VoxelTek/SkyMusicKeypad/companion/companion_assets_rc.py

# Resource object code (Python 3)
# Created by: object code
# Created by: The Resource Compiler for Qt version 6.7.0
# WARNING! All changes made in this file will be lost!

from PySide6 import QtCore

qt_resource_data = b"\
\x00\x00\x19\xc3\
<\
?xml version=\x221.\
0\x22 encoding=\x22UTF\
-8\x22 standalone=\x22\
no\x22?>\x0a<!-- Creat\
ed with Inkscape\
 (http://www.ink\
scape.org/) -->\x0a\
\x0a<svg\x0a   version\
=\x221.1\x22\x0a   id=\x22sv\
g1\x22\x0a   width=\x2240\
00\x22\x0a   height=\x224\
000\x22\x0a   viewBox=\
\x220 0 4000 4000\x22\x0a\
   sodipodi:docn\
ame=\x22SkyLogo.svg\
\x22\x0a   inkscape:ve\
rsion=\x221.3.2 (1:\
1.3.2+2023112521\
50+091e20ef0f)\x22\x0a\
   xmlns:inkscap\
e=\x22http://www.in\
kscape.org/names\
paces/inkscape\x22\x0a\
   xmlns:sodipod\
i=\x22http://sodipo\
di.sourceforge.n\
et/DTD/sodipodi-\
0.dtd\x22\x0a   xmlns=\
\x22http://www.w3.o\
rg/2000/svg\x22\x0a   \
xmlns:svg=\x22http:\
//www.w3.org/200\
0/svg\x22>\x0a  <defs\x0a\
     id=\x22defs1\x22 \
/>\x0a  <sodipodi:n\
amedview\x0a     id\
=\x22namedview1\x22\x0a  \
   pagecolor=\x22#5\
05050\x22\x0a     bord\
ercolor=\x22#eeeeee\
\x22\x0a     borderopa\
city=\x221\x22\x0a     in\
kscape:showpages\
hadow=\x220\x22\x0a     i\
nkscape:pageopac\
ity=\x220\x22\x0a     ink\
scape:pagechecke\
rboard=\x220\x22\x0a     \
inkscape:deskcol\
or=\x22#505050\x22\x0a   \
  inkscape:zoom=\
\x220.14195169\x22\x0a   \
  inkscape:cx=\x221\
718.8947\x22\x0a     i\
nkscape:cy=\x222278\
.9444\x22\x0a     inks\
cape:window-widt\
h=\x221920\x22\x0a     in\
kscape:window-he\
ight=\x221007\x22\x0a    \
 inkscape:window\
-x=\x220\x22\x0a     inks\
cape:window-y=\x220\
\x22\x0a     inkscape:\
window-maximized\
=\x221\x22\x0a     inksca\
pe:current-layer\
=\x22g1\x22 />\x0a  <g\x0a  \
   inkscape:grou\
pmode=\x22layer\x22\x0a  \
   inkscape:labe\
l=\x22Image\x22\x0a     i\
d=\x22g1\x22>\x0a    <pat\
h\x0a       style=\x22\
fill:#000000\x22\x0a  \
     d=\x22m 2356.9\
246,3386.0821 c \
-18.0307,-2.5264\
 -32.8519,-11.32\
53 -38.0379,-22.\
5821 -4.0138,-8.\
7125 -1.2572,-21\
.1465 6.2408,-28\
.15 1.8549,-1.73\
25 8.5143,-6.366\
8 14.7988,-10.29\
83 58.8872,-36.8\
399 186.8723,-14\
3.6695 311.5454,\
-260.0479 165.18\
58,-154.1956 304\
.106,-304.6548 3\
90.3248,-422.745\
8 13.6768,-18.73\
27 46.2035,-66.7\
366 46.2035,-68.\
1885 0,-0.4221 -\
4.4471,-1.0383 -\
9.8823,-1.3694 -\
19.6609,-1.1978 \
-45.9801,-8.0975\
 -62.5415,-16.39\
55 -24.505,-12.2\
781 -42.8529,-29\
.3305 -57.6894,-\
53.6164 -43.2181\
,-70.743 -90.687\
7,-163.2305 -118\
.9184,-231.695 -\
40.9667,-99.3513\
 -63.6331,-187.9\
846 -70.0574,-27\
3.9483 -1.5523,-\
20.7715 -0.6445,\
-75.9041 1.5568,\
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
      id=\x22path3\x22\
 />\x0a  </g>\x0a</svg\
>\x0a\
\x00\x00\x05\xcc\
(\
\xb5/\xfd`\xdc\x1e\x15.\x00v~\xc5&\xe0\xec\xec\
\x9bX\xb4S{\x0e\xaa\x84\xdf`p\x14X'\xfa\x8b\
\x1b\x0c\x82n=@\xc8\x16\xd1\xba\x98\x93\x1d\xc3\x18C\
\x0cB\x08\xb8\x00\xb7\x00\xbe\x00\x95\x0a\xa0W\xe7%\x0f\
\xb5\x06\xec\xcc)\x22$0j\xad\x17\x83\xc4/J5\
\xca\xbc\x8c\xf1\xf5\x96tF\x87\xdd\xc3\xbd\xc4\xf0:\x04\
;\x9e\xa1\xe9\x5c\x92@ \x10\x83\xe1\xe8\xfc?\xd2\xcb\
\xe1\xf7@\xa6ft\xbd\xdaZ\xb5\xa0R\xf6R\xd7Z\
|\xeb-pX\x81y%\xec\xd0\x1d0\xf4\x9b-\xe9\
\x0ez&\xfc\x17\x92\xdeC\x09m4\x07\xdc!\x17\x1d\
\x1dO\xd1K$\xed\x1f5\xa4\x1e\xebD\xaf\xf1\x8b$\
\x88\xde*\xd5iZ\x92\x85g\x9d\x95^\x14\xfc\x01\xd2\
\xe4g\xce\x09\xa0\xf9x\x04\x80\x04\x05\xca7\xbd\xf4\xe6\
%(n\xf0\xfbI\x1b\xd1\x82w\xa1\x97f\x93\x22\x0f\
\xb7\x9e\xb4J\x96^\x9b\x93\xbe\xeb\xcf,9\x14\x0a\x08\
\x01]\x7f\x86\x95\xaa\xe3 \xc0\xa17\xbc\x7fOM\x87\
IE\x8b:)\x13/p4q\xb4\xc0\x932~\xb0\
\xa3K\x0c\xe9\xc9\x8f\x03\xc4\xcbL\xd7\x1fN/]\x86\
\xbe\x8f\x80\xc8\xe8\xce\xbf\x07\xa4\x17\x85\xd0!\x99u\x90\
3\xf9\x0c\x03A\x97dF\xe4\xe3\xd7\x9c\xb9\x18\xa8R\
\x15\xd8\xa4\x86\xec|.&\x89\xba\xf3\x9a\xba\x9c\xd1\xcc\
P\x88\xd2\xf89&\x81\xda\x901)\x9e4\xf4\xea:\
\x04\x96\xd1\xdf\xbawO(\xea\x0a\x92CR\x80\x9cP\
U\xab\xad\xd7\xb2\xd1&A\x18\xdf[o5U\x98\xaa\
\xd2D\x11Z\xb5\xc2\x96\xc3y\xc5\xc6kQ\xec \xc7\
t\xbd\x09\xf5\x18Vz\x81\xb8\x08\x8e\x1e\xc4GO\xaf\
\xd0'\xb9\xeeZ\xec\x1c\x13\x92\xaf\x9aT\x1e\x94\x88\xee\
\xcb\xb0\xccI\xbc/gZg)\xcc\xabl\x1b6E\
0\x8a\x86'\x0f\xcc\xbb\x0d\x1cF\xb1\x5c\x86T\xdbY\
8L\xd2}\x13\xec\xe2q\x9a\x83\x15\xc1y\x99R\xc9\
\x91/\xcb\x12\x88\x97\x1b\xba\x86\x07\x91\xbd\xca\xdb2\x87\
Y\x0c\xb8\x9cq\x95\xc7\xf7\x905\x87o\xa2a^\xce\
\xa8\xbci\x93/\xb2i\x9ew\x81|[E\xf3 \xb9\
\x1b\xb0\xd3\xa2a\x1bUU+\xfd\xc1\x92^\x9c\xce3\
~\x83\xfdkJ\x8d\x01K\x91s:\x1e\xde5\x1a\x9f\
\xa9]w@\xcbWj\x91S\x08J\x8e\xe1\x84\xfcT\
\xe7\x84\xef4\xb8\xf4\xd2\x9b,\xafT\xe95-\xa6\xa8\
\x9c\xd3lP4\xb4\xbf\xecJ\xd7\xb5\xf7\xd0\xcb\x7fr\
_\xc6\xf0\x83\x92\x1d\x00\x09\x9a\x8fg X*Ra\
\xa8\x94\x04\xe2a\x12+O\x1eZ\xa79lZc\xaa\
&\x83\xdca\x0fjs\xf2\x87\x9e\xfe\xfd\xe6\x90\xbfI\
n\xd1\x5c*\x04\xf6\x0e\x8e\x1e\x14\x0dl\x03[\xbd\xf9\
vXGT\x96dF\xe2\xe2\xa9a'\xb6\xa4\x0a\xcf\
\xc9\xb4\xf6\xdak\x17urfE\xb4\xa8\xf7\xcerF\
3Z\xdc{\xadkI\x96\xc5\xd37\x86_o\xba\xc9\
\x01o-\x8a\xa4\xe4\xe2o\xe3\xb2\xe7a\x16\xebmZ\
\xc5\xf2A*]\xa7E2W\xf1\x05by[\x8el\
\x98\xd7x\xa8d\x95\xe5\xf2e[~|\x13\xcc\xcb\x14\
/gI\xc3\x83\xfa\xa6\x9b\xb3\xca\xc4\x02\x91\xf1\xbd\xd9\
\xc3\xdez;\x0d\x02\xfb,\x08\xb6\xc0]\x1a[\xce2\
-\x81#\xa8\xf18\x87\x18\x9a\x99\x11I\x92$m\x06\
\xa1\x08!\xd09\x0d\x8f:BQ\x92\x82Q\x92\xa1@\
\x0a\x11D\x08\x13$\x81\x88\x88H|\x12\x88H\xe0\x07\
\xc45=\xe0a'-\x9a\x0e\x93\xbf\xe9\xa0\xdb+\x1e\
k\xdc\xaa)\xac\x18\xf5\xc1\xd0\x81\x85\xe6\xe6I\xccV\
+\x7f_\x1d\x91jhh7\x93\xf3\xd3UK\x8a\xf7\
\xfb-C4\xed\x94.\xa7\x9cC\x1a\xb4\xe7\xd0E;\
\xc4UN\x0f\xab\x83~\xd6V\x1d(X\x83\xd1!\x8b\
\x03\x90\xd3\x92| ^\xd5\xdb\x95\xb4\xba*\x96lv\
\x8dk\xac_\x89\xecD+-\x9b\xdf\xa9\xa2:\xa6<\
1\xe6\xc1M\x95\xb3,\xe4\xaa[\x96\xe0\xbb\x8dX\x5c\
i#\xb0;\x0b\x02\x06L\xe6\x1eG\xc5\x0a{\xb9\x8b\
K\xc7\x02\x93\x0d\xe5s-\xcf\x19t\xdc\xfe\x88`\x93\
\x1a\xf3\xe5\xd2\x04J\x87\xed\x06Q-\xa7\xd3\x01\x8b\x15\
)\xfesp\xf8C\xe1\xb9\xd3\xc1\x94\xf8\x96\xd9\x7f&\
\xc8\x03\x83]FG\xe3\xd5\xa0\xa2\xa0\x00S\xc0\x04\x8c\
[\x1aC\xe7\x89\x0e\xc7\xe9\x02\x95\xb6\xd9\x08Q\xde\x5c\
\xf3\x96\x85s\x96\xd8\x81\x89sd\xafq\x17\x87\x11\x00\
\xce\x15\x96(p\xae\x5c\xa1\x14h\xf0\x0b\xf5\x98\x8a6\
\x07i\xa8\x1f-\x1cS\x94 v\x86\x17\xdc;\x86\xd1\
\x1ck\x8839\xc4q\x85\xcaID\x90\x901\xca\x9a\
]0P\x17\x1d\xf8(}\xa5\x0e\x84\xce\xf8#\x13\xc8\
\xe1>\x85\xef\xee\x0d\xe0\xef\xa5s\x8d\xa1W\x83\xf0b\
\xd1\xe2\xcf\x834\xfa\x00i\x97\xc0\xe0o\xa4ur\xc4\
\xc8\xb3\xf0\xc3\x01\xca\x8f\xdcR\xdbT\x93\x18D\xc1\xe1\
\x85\xaf\xd2\xa7\xe5\xf1\xd3\xeb\xf5\x1f\xc9\x05ZV\xc2\xef\
\xd1^}\xaf\x13\x92t\x18\xea#\x84:\x16\x82\x93\x5c\
\xefpK\x81\xac\x00 $\xa7\x87\xca\x03\xff\x11\xa0\xb6\
HEC\xcf[`I\xb9,z\x0a\xd6\xedB\xd1\xfd\
+vY\xde{\x80;\xfd\xd0g\x98G\xe2E\x883\
X\x1e\xfb\xb4\xf4\x0ed\xc4A\x1e>\xf1\xf4\xce\xc1\x94\
5\xdes\xa9=\x00>\xed\x89\x0e5|2\xbb\x02\xb4\
nFL\xfat\xbd\x1d\xff\xc0 \xd7\xa6.\xab!\x93\
\xfa\x15\x94\xcb\x5cy\xd2\xden\xf0\xe5\xbb`\xe5L9\
\x9b\xb1K\xb4\xb3t\xb3eF& \x00!\x152\x17\
x\xf3T\xa4P\x96\x93\xc9\x987\x06f\x81\x14\x80'\
\x93&6*$O\xe6\xbc\xb9\x08|\xe5\xf1 \x87\xcc\
DX\xb2\xfbm-#\x98\x86M\xa5\xb2qx~\x86\
\xe8\xba\x7f\xd0hb'L\x88\xbb3\xfb\xa0\x00\xa6D\
\xd1?PG\x83\x1c\x22n\x12ch\xf8\xe6=\xe5p\
\xec \xab\x1f\xfe\x09\xa9D\x81b\x8a1\xba\xa2\xb2\x8d\
4\xb8\xe7\x17f\xa3\x06c\xc2u\xe89\xcd\xf4\x89\x86\
0_\xd4A,\xaa;\x10\x98\xad\x02\
\x00\x00\x05\xf3\
(\
\xb5/\xfd`\xc0\x1fM/\x00\xe6\xbf\xc9&\xe0\xcc\xee\
.\x15,+\xad\x92\xaca\x19hq\x989\xfc\xc5\xd8\
\x8f\xd7{c\xe3\x01v\xd3.F\x08\xc9\x8ea\x8c!\
\x06!\x04\xbc\x00\xbd\x00\xc3\x00\x7f\x8f\xdf[,\x15P\
\xb1\xefK/n2\xdcP:\x22$,\xac\xb58{\
\xc6s\x94l\xa4}\xda\xe2\xdc]\xda\x97-~\x8e7\
\xa5\x85\xb9\xc5pc.\xc8\xef%\xc9\xe3\xf1,\x16\x8c\
\xcdyb*\xc60\xfb\xc0\xc5^\xb6\xc5\xfb^\xb6\xc0\
R\x17S\xf8\xde\x8c-.`\x5c\x01\x8a\xa5\xcc\xd8\x9b\
P43]\xda\xa5\xf8\xb9\x08\x8a\xdc\xe4H(2[\
\x13v\xd1\x8f\x8c\x8dIUl\xe4\xf7\xc4\x90|c\xec\
T1\xcc9rO\xc5V\xb2\x13\xbd\xa4+SKm\
\xc5>\xbe\xe1\xd9\xbcC)\x05 ;&\x02@\x82B\
\xf5\xbdb\xbb\xfb2\x1c{x\x9a\xb4Z\xd1\xc2W\xa9\
\x18\xd9\xf9\xe8\xc5\xbei\xb5\xd2\xadX\xf7\xdc\xfc\xbbC\
K\xcdG\x01!\xe6\xc9{\x05#\x9e!\xa4\xff}.\
\xaed\x19\x076\x80\xb13\xfe\x9f&E\x1d(\x15A\
\x96Jh\x86rDs\x04e*\xc1\x9c\xe1f\x97\x16\
n\xf2\x0e\xc3\xe3\xcb\xcb\xdf\x1d_\xb1]R\x9cf\x04\
\xc4e\x7f\x7fr\xc2\x8aU\x88-r\xed\x87\x9a\xc9\xbc\
,\x10v\xc9/\xa3\xc7\x9c[C\xa1\x01+Y\x81\xce\
I\xfe=\x85&\x89\xc2\x14\xa3\xbb\xa4\x11\xbd|F\x09\
szKB\xbd\xe2\x82\xd6<\x91\x15\xfb\x9b\x22,\xa3\
\xb3\xef\xff9\xe2\xb8+\xb8\x86\x7fB\x0dEe\xed\xb5\
\xf8\xbaQ\xe7\x9e\x9c1\xb6\xb8\x9a\xaaLYi\xfa\x88\
\x97\xad\xf2\xd5x_\x911\xf78\xfe\xd0[\xfe\xce\x88\
\x1b#\xda\x8ay\xfc\x18bL\x8f\xc7\x98\x15\xa38\xb9\
\xdf\x01\xe0\xe5\xc8\x16\xba\x8a\xc5iM\xdb `\x15\x99\
4$\x11\x1e\xa8e\xba\x83|\xa0\xd66\xefR\xd97\
\xe1\xb8lzd\x92-G\x1a\xd9\x87\x1b\xbaLr;\
\xed\xb0\xd7\xa3t\x19\xc4\x03#Y\xe5\xeb6\x87+\xa2\
\xfb\xb4d\xa2\x1f\xa0\xa6!\x8eO7x\xd6\x07\xa1\xbf\
\xea\xe3t\x97Q\x0c:\xadu\x93\x06\xf8\xa07\x070\
\xb2e\x9f\xd6(\xcdm\x11\xf0\xc1m\xdfWq\x80\xdc\
d\xfb\x1c\xda\x1b\xb8\x13d]\xab\xaal\xb5\xcf\xb0\xac\
\x98\xe6\xfb\x8b\xd9\xc3\x7f\x92\xe5\xb6\x84e\x1d\xbdf\xc3\
\xf1\x9f$\xcd\x8b\xfd{\x13R\xc0r\x8f^BPz\
\x8b\x86\xc2\x9c,\x9d2\xa6\x06x\xff\x903\xb1;/\
\xb1d+6AST\xd2\x89Z\x1fk\x9b\x95>\xf1\
\xfe69\x15\x0b\x00\x09d\xc7\x5c \x5c\xea1a\xb0\
\x14\xc4\xf1e\x90KG\x1a\x9b\xb79p\x9b5U\x93\
\x81\xf6\xb2\x06\xd5=?EN\xf7\x8e\xb3sO!'\
\xeaR\xd4\xdd\xddw\xc6eDe\xc9/\x12\xf4\xb2*\
\x8a\xb2\xf9\x92,\xca\xb2*\x9c\xe9\xbd\xae\xadr\xbe\x17\
\xb2TC+\xe8\xbdQ\x04Q\xd9R!\x85\xaak)\
\x84-{]\x93\x84/\xcd\xe8e'\xa9\x820\xc6\x17\
\xbe\xa4\xeb\xe6\x09\xc4\x88\xe7\xcex\x93C\xee{\x1c9\
\x04g\x90\xeb\xf4\xf7e\x94\xfbq\xdb\x84\x02:&\x9e\
\xb7=tgs\xc5q}\x9c~p\xd9g=L\xb4\
\x8aR\x015N7\xc0H\xf6i\xc9\xa75\xa4\xa1A\
\x81\x13\xd6\xda$B\x81\xd0\x19c\xadq\xb1\xc5\xde\x06\
\x91\x05\x81/\xa8\xf18\x87\x18\x9a\x99\x11I\x92$m\
\x06\xa1\x0c1\x10:\x0b\x8f:2Y\x14\xc2A\x12\x81\
@\x08\x19D\x08\x13$\x81 \x12\x88H<\x22\x12H\
\xe0\x07\x84*= a\xef\xee.\x1d\x83\x1f\xae\x92.\
\x5c<\xa0q\xc1\xd1t$\xea\x83\xc3\x93\x1e\xce\xddN\
\xc2\xbd\xccQ\xfd*\x17:\xa3\xe1\x1e\x82\xdc\x86\x19\xca\
<1\xdc\x02%\xcd\x08\xfa\xb4\x98T\x11<\xa7\xe5&\
\xdb\x87{\xad\xcc\x5c\xfe\x08\x0a\xe1j\xea\xb8\x03Wq\
\x0b\x11\xbe\x7f\xcd\xf0\x0d\x80\x0e\x96\xa2\xfc%\x93'9\
NJ6\xd3O\xab\x22~\x898\x10fk)j\xa0\
\xc4h\x09\xb9&&\xbb\xc9\xef\xb4d\xb7J\x1eq\x99\
\x93\x92\x9cH\xd2\x9dRQ\xc7\xd4NX\x14P\xbfb\
!\x0bi\xeb\xaa\x12V\xb7Q\x11\xd7\xd9\x08\xef\x0e\x83\
\x80\x01\x99\xb9\xc6Q\xb1\xc9^\x0e\xe2\xd2\xb1\xf8dP\
\xf9l\xc8sL\x8f\x1b\xd2\x11\xde\xa4\x06x\xb9\xe4\x02\
\xa5\x1bu\x83\xa8\x96\xd2\xb9\xc2\xc2/\x05\x7f\xce\x0e\x7f\
('77\x98\x19\xdf2\xe8\xcf\x1ay`\xb7\xcb8\
\x1a\xdd\x0e\xe2\x0b\x080WL\xc0\xb8\xa51\x5c\x9e\xeb\
\xe10,P\xc96\x1b\xf9\xe4\xcd\x95\xec\xb2\x18\xce\x12\
V0\x81B\xf6\x1av\xbd\x8c\xb0pxY\xc2\xc2\xf9\
\xe5\x0c%\xa7\x11\xbcP\xa3TPs\x90U\xfd\xb0\xe0\
\xd0\xa2\xc4n\x87{\xa1\xbbc\x1b\x8d\xb1\x06q&E\
\x1c\xa8P1\x89\x0a$d8\xb6f\x17\x8c\xf4\xa2\xcf\
\x1f\xedW\x8e\x81\x10\x92\xc7\xbc\xe4\xd8\x81B)xc\
\xd2h\xa5_0-q\x90\x97\x8f\xf6?\x0f\xddt\x0f\
\x09.\x81\xd2oPu&\xec\x96'\xf4\x87\x03\x88~\
\xf8\xc1Q3I\xf2\x16\x14\xbd0/z^>>\x9d\
Y\xffa]P\xcc\x8a\xe8\x1eU*\xe8u\xe4\xd2\x84\
\xa1&Bwc!\x89d\xf8\x8e\x99\x14 \x05\x22\x22\
{\xfa\xbd|\xfd\x1f\x05UG\x8a=\xf4\xb0\x05\x97(\
p\x15\xd2Y5\x17j\xe9_\xcc\xe2\xbf\x17\x01w\xc0\
\xad\xcfj\x1e\xce\x8b\x18N\xa1\x5c\xe4S\xd5;\xdc\x10\
\xc7\x9c}\xe2\xf0>a\xaaoT\xa4[[\x06\x1f\xf8\
\x84\xec\xfa\xbd\x9f\xdd\x00\xad7\x22fu\xba\xe2\x8eH\
\xc1@hS\x99\xd5\x90L\xfdzr\x99/'m\xde\
\xcd\xb3|GVd(\xa73\x96\x01\xbbJ\xb7\xa3\x8c\
\x07\x04\x06@\xa4\x22u\x01`\x9e\x0c\x8a\xa4\xe5\x04\x18\
#\xc0\xf0Y\xf8\x01\xae31b+G\xf2\xcd\x1c\x98\
\x0b\x91\xaf=1\xe4\xcc\xcc\xad\xa5\xc4o\xe6\x0c\xcc\xb4\
\xc3\x14\x94\xb5\xc1s0\xc4\xeb\xc4\x84\xf6\x09\x8b\xf0/\
\xee\xf6\xec\xa0\x05<$\x0a\xf8\x01Y4\x06\x90b\x93\
\x989\x0d\xab\xbc\x8ar\xe8:(\xecG\xfd\x84\x07Q\
\x00\xac\xf8\xa0\xaeT\xb6\x93\x82\xfb|\x03\x9ck\x94L\
\xa8\x0eK\xa7\x1e\xfd\xd3\x10\xfe\x0b6\xc8NE\x07b\
\xb1U\
\x00\x00\x06;\
(\
\xb5/\xfd`\xe1 \x8d1\x00JB\x08\x0d)\xc0j\
\xec\x0eC\xf32\x1a\xb8)\xffY]\xabe\xb0\x5c\x8f\
\xfet\xd9%\xde;\x95\xd2\xcfeY\xe8\xed\x0a\xaa\x08\
\xb0,\x82\x00\x83P.\xc4\x00\xc3\x00\xc9\x00\x98\x0e\xfe\
9e\xc6\xb0o\xbf=\xdf\x19h\x0e0'\xdf\xc5\xde\
\xed\x8f\xb3H\xe9!$ (\xa5\xf6b\xbc\xd1{\xa8\
Si\x15b\xdc\xfc\xd9\x94\xdd\xf9K\xff\x0f\xe2\xef\x8e\
\xb3|\xc4\xe7\xfb\xf3`0\x18\x04Ba\x19GpN\
\x8a\xcf\x07P(eS\xbb\xabD\x0b\xd0\x5cm\xb6\xb5\
^Km\x01E\x15 \xeds\x15\xdb\xc2u\xbf\x81?\
\xe0\xd8\x19\xb6.\xfc\x17H\xa6aW8\xdeuOa\
\xf9yN^XG\xf0\x0b7H\xf1\x9c\xc0\xd1\x0b1\
\xd3\xd2\x87b)=\xd2\x95T\xd29=\xf4\x05f\x87\
\x0eRJ\x00\x9f\xc3G\x00\x90p`v>\xa7\xcd\xbb\
\xc8y\x9c\x1b\xbf\x9c\x91\x83@\x9b\xcc\xe9\xe3\xa1\xd7;\
\xbe\xe5\xa4O\x9d\x13\xef\xe1\xf7\xdbA\x8a\x95\x87\x03\x08\
\x01\xd1C\xb4\xff\x84G2\xbf\xffeN\x7f\x0c\xf9\x04\
\xecF\xce\xc1\xfd\x1e\x11\xf5\xa1\x0a\x034\x80b7t\
?\xfe,\x15dv\x1a*!\xf26\xd7\x91\xd7i\xae\
\x84\x80#g\xd9\x22C\xf8C\x07\x05\xa6\x8b\x14\xbf\x1d\
\xfa\x9c\xb6\x98\x19?\x03:\xa7\x05\xca\xf6}\xbcps\
\x9a\x0b\xbb\x0b+\xcfU\xf0\xa7 \x10\xb6\x18R\xbc\x0e\
\x8e\xbb\x22\x9b\x01\xf4\xa1\x02x\xf8\x85\xbe\xcb\x06?\xd9\
\xcaInQ:\x92\xf2\xe0%\xcc\xda!\xe47'\xbf\
3\x9c\xe8\x8c|{\x7f\xe9\xbc\xfd \xac\x84\x0f\x5c%\
\x03QZ\xa9\x95\xaa\xc3C\x0c\xae\x11\xc5\xf9\x812\x96\
JP\xad\x0f\xbeNwq\x8e\x129\xf1\xe49Uz\
\x7f\xd0\xf0\xb7\xe7y\xae3\xf8\xdd\xd0m\xb0\xa3s\xc2\
t\x8f\x03\x7fy\xc3VW\x91\x87dA_k\xabE\
\xb5\xd4f\xd6\x02\xb5I\x0c\x0a\x016\x89.]U\x96\
c\x83\x1e\x91\x05\x84A\xb6U\x94\xc6\x1c\xda\xa6++\
\xab\x99\xd2\x22\xd7E\xe1\x06\x05\xb1\xeecAiV\x01\
FA*\xa6\x19\xb4f\x12\x8crd\xdb\x83\x9ah\x98\
\xa5 1\xc04\x0d\x89\xe8\xc6Vi\x07C\xd3\x0a\xb2\
H[\xd0\x1a\xa4]\x1a\xa3$\x09LWXd\xb1-\
\xd0\x96\xc2\xf6\xb0(MWY_\xd6ck\x5c\x96\xa6\
M\x18\xdb\x15\xb14\x86\xce\x06T\xdcD5\x82 \x0a\
\xed\x91\x13\xe7T\xf1\x9d\xf29\xe7\xc7O\xdc\x0c\x9c8\
\xe7T\xb1\x5c\xba\xff\xbeO\xa1~[8\xc9&n\xaf\
C\x08\x88\x9d\xa1\x92\xf9\x98J|\xadL\xd8\xed\xb9\x8b\
\x83\xcdC\xd1>tN\xb8\xc1\x8e(\xb1\x0c\x00\x12>\
\x87\x8f@\xa8\xb9\x11I@\xb3\x83\xa1Q\x0eI?\x16\
Vf)\x5cV\x84!\x9c\xd0\x19\xb5\xc8\xbc\x87cw\
\xe1\x9d1\xf2\xb0K>lk\xcdY\x8a\xa0\x9c\xa3\x1c\
E\x90\xbd\xb2J\x95B\xf7\xd6\xea8M\xbe\x99\x83*\
\x95\x8d\x8d\xa8$\xe1\xc7VII\x89\xe2\x07\xca\x19\xce\
{\x0e\xfc\x9c\x97\xa8\xd1\xad\x9bw\xae\xa8\x0aG\x14C\
J\x03{qT\xe5\x95\x1e\xe8\xca\x87\xac\xd5V[\x1b\
*+\xf2\x81\xd3Pk\xa5(\x1d\xe94\xd6Z\xc9J\
\x8fT/\xde\xc0n\xdc\x0d\x19V\xb8|{^\xe8\xb0\
w\xbb0\xadi\x94\xa4j\x97\x15\x91l\x8cH\x96Y\
\x0d\x8d\xd1;aH\xda\xa5\x1b\x17\xa5E\x0b\x22\x15$\
\x99l\xd5\xa5\x17\xdb\x83\xd24D\xd3\xda\xa1`\x11\x81\
B\xa8\xf1<\x87\x18\x9a\x91\x11I\x92$m\x06\x91\x08\
1\x10:\x0d\x8f:BY\x16BY\x10\x82 \x84\x8c\
!F\x09\x92@F\x02\x11\x89GDD\x827\x84\xaa\
\x1e\xf0\xb0\x99\xf8\xad\x0e\x17\xcaM\xcaMO\x8f\x8d\xb9\
\xd6\x89L\xc0\xfa\xb8w\x1b\x83\xdf\xa9I\x02\x8c]\xaa\
\xee\x95R\x9c\xa2\xb9=\xc4\xbf-ER\x06<iK\
8\x07g\xaam'`j\xce\x83\xc0]\xd4\xf8\xea\x8e\
\xff\xa4\x02|GZ}\xd2\xc8I\x01\x91Y\xb0g\xb3\
\x03TW{\x7f\xcb\xc7G\x14;k\xa5\x930\x8e\x1e\
\xbb!t'8o\x1fy\xae\x14l{\xe2\x94\x0d\xfd\
\x9ao\x18\x91K\xcc\xd2L\xa5\xd3\xce\xe7\xa5\x22\x1c!\
p\xdf\x0c]\xdfM\x5cu\xec\xe1\x03@\x15\xb5\xa5\xa6\
+X\xbd(\xe5\x8a0@\xa2\xfd:\xa8\x0b\xea\xae'\
\xa9Z\xc9H\xc0,\x01\xd7\x98\xd22\x9a\x13-E\xf2\
\xbfS\xdf\xd71\xfd\xe4\xf2\x07\x95\xaapc!\xe2n\
B\x82\xef6\xd2\xc8\xed\x14\x04w\x17\x84\xa0\x01\x999\
\xa9Q\x01\xc2^.\xe3\x0c\xb2@\xc9w\xf0\xb9\xc8s\
\xb6#7\x88!\xac\xa9\x86\xd4\xbe\x8c\x02\xa5{\xdb\xb0\
\xae\xf6\xce\xb5c\x81\x8cB\xa3k\xe8\x1fj\xc4\xe9\x1d\
\x86\xe4[\x8c\xd6\xe7G\x0f\x04p\xa3\x89\x9e\xb8\x83<\
J\x00\xe60\x09\x98\xb50\x86\xe3\xcd#\xe7\xc3\x02\x95\
\xb6\xd8\x08\x91\xde\x5cs(\x0b\x9b,\xb1\xb0\x09Dc\
\xafmg\xa2\x084\xf7D%\xda\xdc\x13\xd5\xa3p\x1b\
\xc0\x81\x9aU\x05Q\x07\xb1\xbe\xc7\x84\x1b\xc9%\xaf\x1d\
\xc9\x05\xc2]\xaeh\x80\xf5\xab\x99\x1crtY\x05\x12\
\x11\xac\xc8X\xc6\x86\xb8`x\x8e\xf6}\xb4\x9fR\x07\
\x84\x001&B\x8e\xb1\x0c\xd6\xff\x8dA\x82J\x7f\xc0\
d\xbbI\xb0\xc6\xf4\xe5y8\xa5\x84K6%h\xc2\
\x1b\xea\x1dU\x82\xe1\xc1\xe6\x81\xf4\x90?\x8a\xe0\xe8\x99\
$\xbb\x05\xe5,\x8c\xd36\xc8C\x9bV\xc1\x7f\xf0\x16\
\x14\xb7\xa2\xc6\xa3\xa4\xfa\xbfNP\x12\xccP\x1b\xa0;\
\xd2\x90\x88d\xee\x0ee\x0a\x10\x03a\x02;=\xb0<\
\xc3\x1f\xf5j[\xaa\x15*N\x0bT\x10\x0d'\x13-\
\xb7\x16U\xff\x90\xac\x09\xfc\xbe\x10\xb8\x0b\x1e5\xd3\x0b\
\xb1w\x86\xcc\xc3\x98\x16\xb5#DL\xe2\xc6\x1b_\xe3\
\x9c\xa7\x1e\xe2w\x17\xb5\xd3\xe4\xfb\x9e\x88\xa8\xae[\x9b\
\x03\xec\xea\xbaah\xd2\x5cuB\xae\x0d\x1an\xbe\xbb\
\x01R\xf8\x89\xfd\x1fA/\xe32\x90\xb6\x909\x1f\xdf\
\x1f\x8a\xf0\xc9\xc9\xca\xfa\x0b\xe9\xf9Q\x18\xe1Q\xd8-\
C\xc8v\xb9\x5c.\xa01\xd2\x18\x9e\x0b\x06 \xeaL\
\xbe\xb19\x9340'\xc9\x05\x87\xd7\xcc\xf8x5\x17\
ji\xe16X\xa6\xf3\xcc6\x1faW\xf3\x8c\x07\xd1\
;\xf1\xd1>Q2\xec\xc4\x9dG\xbb\xda\x80\xa4D\x09\
?@EFa\xc4\x8a\xf6\x05\xcf!(V\x84B\x98\
\xe3S?b\x0e\xc8\xac\x82d\xc5d\xe5Te\xf9\x0b\
\x1a\xdc\xbf\xf1\xde6\x00\x89G\xc2\x0c\xc8\xa3o\x182\
\x7f1\x0e\x0a)\xcb\x81\xa4k\x15\
"

qt_resource_name = b"\
\x00\x08\
\x0c\xdf\xacs\
\x00k\
\x00e\x00y\x00I\x00c\x00o\x00n\x00s\
\x00\x04\
\x00\x075\xdf\
\x00l\
\x00o\x00g\x00o\
\x00\x06\
\x06\x8a\x9c\xb3\
\x00a\
\x00s\x00s\x00e\x00t\x00s\
\x00\x0b\
\x05\x96\x06\xa7\
\x00S\
\x00k\x00y\x00L\x00o\x00g\x00o\x00.\x00s\x00v\x00g\
\x00\x13\
\x0f\x14:\x07\
\x00s\
\x00k\x00y\x00M\x00u\x00s\x00i\x00c\x00_\x00s\x00q\x00u\x00a\x00r\x00e\x00.\x00s\
\x00v\x00g\
\x00\x13\
\x01\xb6*\x07\
\x00s\
\x00k\x00y\x00M\x00u\x00s\x00i\x00c\x00_\x00c\x00i\x00r\x00c\x00l\x00e\x00.\x00s\
\x00v\x00g\
\x00\x11\
\x0e|\xc8\xc7\
\x00s\
\x00k\x00y\x00M\x00u\x00s\x00i\x00c\x00_\x00b\x00o\x00t\x00h\x00.\x00s\x00v\x00g\
\
"

qt_resource_struct = b"\
\x00\x00\x00\x00\x00\x02\x00\x00\x00\x02\x00\x00\x00\x01\
\x00\x00\x00\x00\x00\x00\x00\x00\
\x00\x00\x00\x16\x00\x02\x00\x00\x00\x01\x00\x00\x00\x07\
\x00\x00\x00\x00\x00\x00\x00\x00\
\x00\x00\x00\x00\x00\x02\x00\x00\x00\x01\x00\x00\x00\x03\
\x00\x00\x00\x00\x00\x00\x00\x00\
\x00\x00\x00$\x00\x02\x00\x00\x00\x03\x00\x00\x00\x04\
\x00\x00\x00\x00\x00\x00\x00\x00\
\x00\x00\x00~\x00\x04\x00\x00\x00\x01\x00\x00\x1f\x97\
\x00\x00\x01\x8f\x94\xf4\xd9\x17\
\x00\x00\x00\xaa\x00\x04\x00\x00\x00\x01\x00\x00%\x8e\
\x00\x00\x01\x8f\x94\xf4\x8b\xab\
\x00\x00\x00R\x00\x04\x00\x00\x00\x01\x00\x00\x19\xc7\
\x00\x00\x01\x8f\x94\xf4\xb4\xab\
\x00\x00\x00$\x00\x02\x00\x00\x00\x01\x00\x00\x00\x08\
\x00\x00\x00\x00\x00\x00\x00\x00\
\x00\x00\x006\x00\x00\x00\x00\x00\x01\x00\x00\x00\x00\
\x00\x00\x01\x8e\xf5\xff\x046\
"

def qInitResources():
    QtCore.qRegisterResourceData(0x03, qt_resource_struct, qt_resource_name, qt_resource_data)

def qCleanupResources():
    QtCore.qUnregisterResourceData(0x03, qt_resource_struct, qt_resource_name, qt_resource_data)

qInitResources()
